susundberg/zephyr-robot-supa2019/3d_parts/stl_files/robot_motor_small_v0.stl

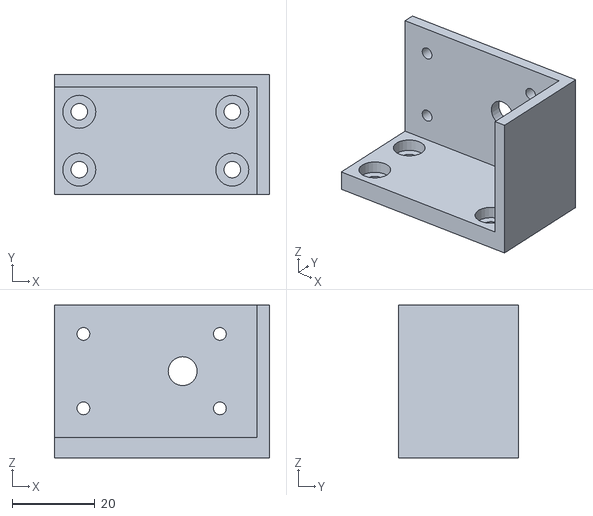
[picture p15: CAD file, 2020-02-02]
3d_parts/stl_files/robot_motor_small_v0.stl
52.0 x 29.0 x 37.0
