susundberg/zephyr-robot-supa2019/3d_parts/stl_files/robot_bumber_mount_f_v0.stl

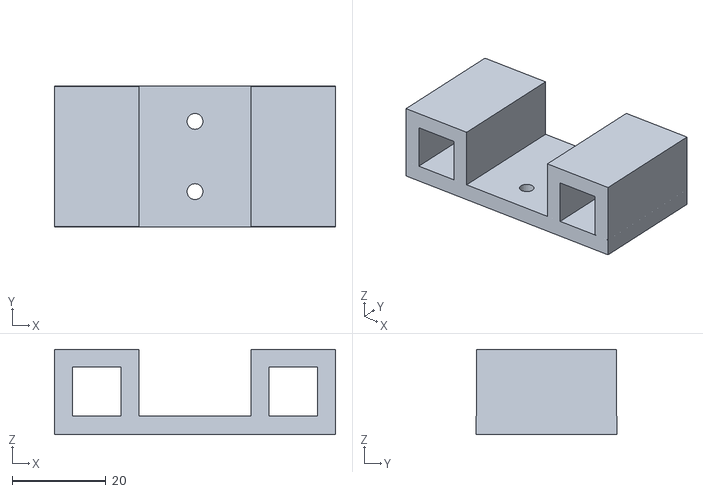
[picture p16: CAD file, 2020-02-02]
3d_parts/stl_files/robot_bumber_mount_f_v0.stl
60.0 x 30.0 x 18.2
