susundberg/zephyr-robot-supa2019/3d_parts/stl_files/robot_supp_mount_v1.stl

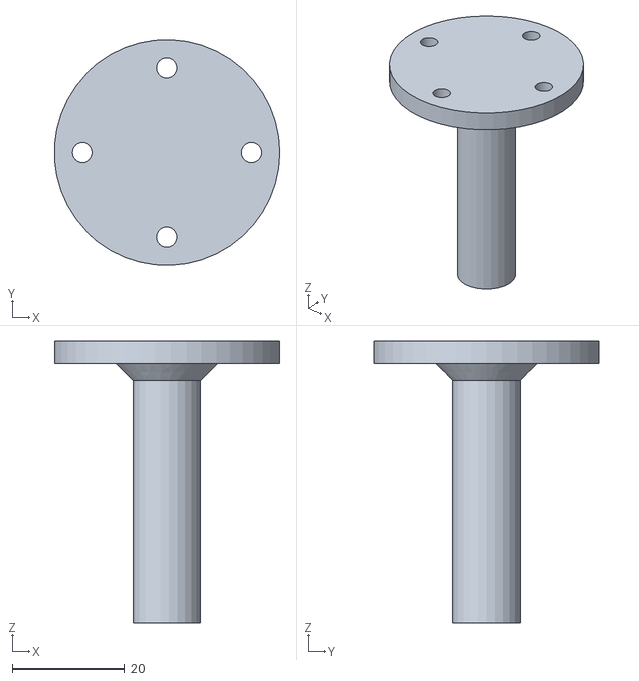
[picture p17: CAD file, 2020-02-02]
3d_parts/stl_files/robot_supp_mount_v1.stl
40.0 x 40.0 x 50.0
