susundberg/zephyr-robot-supa2019/3d_parts/stl_files/bmotor_pads_round_v0.stl

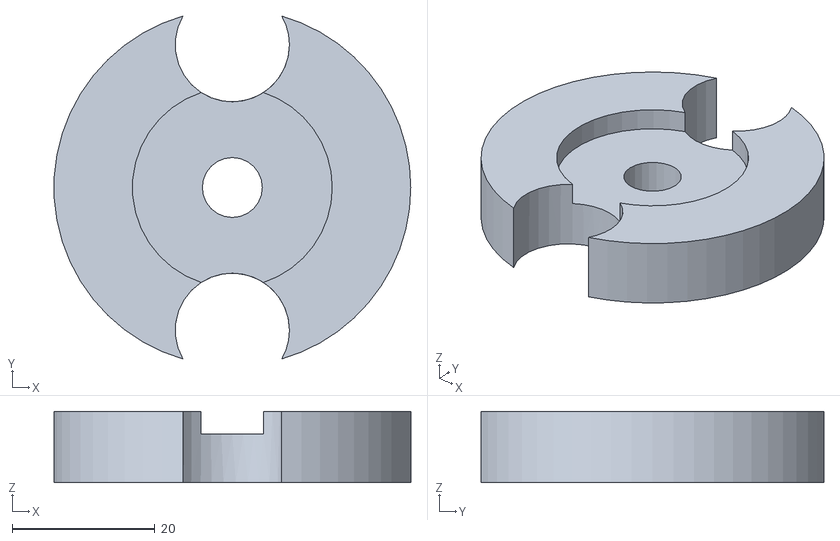
[picture p18: CAD file, 2020-02-02]
3d_parts/stl_files/bmotor_pads_round_v0.stl
50.0 x 48.0 x 10.0
