susundberg/zephyr-robot-supa2019/3d_parts/stl_files/robot_bumber_bumber_v0.stl

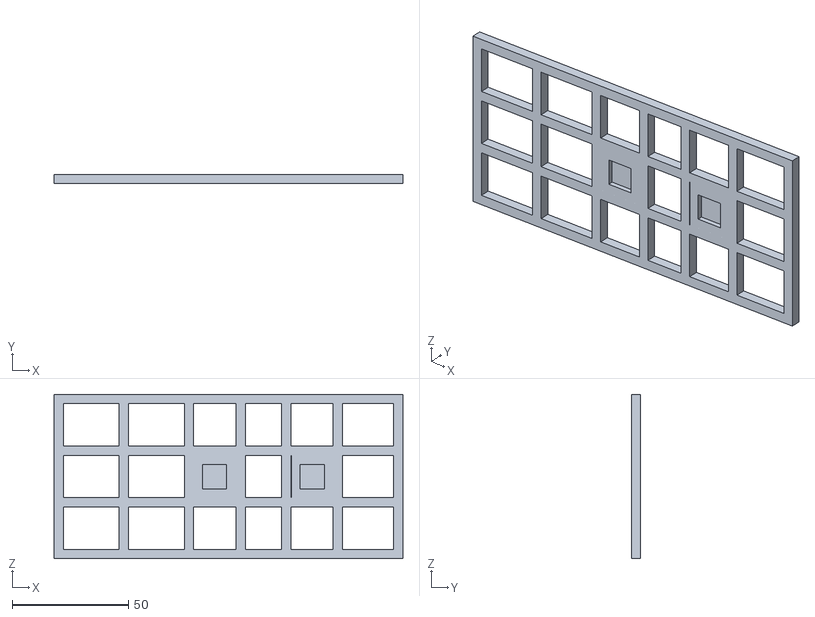
[picture p19: CAD file, 2020-02-02]
3d_parts/stl_files/robot_bumber_bumber_v0.stl
150.0 x 4.00 x 70.6
