susundberg/zephyr-robot-supa2019/schematics/kicad/TMP.sch

## KiCad design schematics/kicad/TMP.sch (2020-06-10)

Schematic: TMP.sch

Parts:
C8: 0.1uF; C_Rect_L4.6mm_W2.0mm_P2.50mm_MKS02_FKP02
C10: 10uF/10V; CP_Radial_Tantal_D4.5mm_P2.50mm
F1: Fuse; Fuseholder_Cylinder-5x20mm_Schurter_0031_8201_Horizontal_Op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
J1: CONN_POWER_IN; TerminalBlock_bornier-2_P5.08mm
U3: LM2596_DC_DC_BUCK_MODULE
U4: LD1117S33TR; TO-220-3_Vertical
