susundberg/zephyr-robot-supa2019/src/motor/motor_ramp.c

#include <math.h>

#define SUPA_MODULE "mor"

#include "../main.h"
#include "motor_ramp.h"

LOG_MODULE_REGISTER( motor_ramp );

#define MINDIFF 0.00001f


static float sqrtf(float square)
{
    float root, last, diff;

    root = square / 3.0f;
    diff = 1.0f;

    if (square <= 0.0f) {
        return 0.0f;
    }

    do {
        last = root;
        root = (root + square / root) / 2.0f;
        diff = root - last;
    } while (diff > MINDIFF || diff < -MINDIFF);

    return root;
}



static float motor_ramp_acc_solve_max_speed( float distance, float max_acc )
{
    const float scalar = (2.0f/3.0f);
    return sqrtf( scalar * distance * max_acc );
}

static float motor_ramp_acc_solve_distance( float max_acc, float speed_diff)
{
    const float scalar = (3.0f/4.0f);
    return (scalar*speed_diff*speed_diff) / max_acc;
}

static float motor_ramp_acc_solve_time(  float max_acc, float speed_diff )
{
    return ( ( 3.0f * speed_diff ) / (2.0f * max_acc) );
}


static float motor_ramp_acc_speed_i( Motor_ramp_acc* acc, float t)
{
    return (1.0f/3.0f) * acc->const_A*(t*t*t) + acc->const_M * t;
}

static float motor_ramp_acc_location_i( Motor_ramp_acc* acc, float t)
{
   float t2 = t*t; 
   return (1.0f/12.0f)*acc->const_A*(t2*t2) + 0.5f*acc->const_M*(t2) - acc->const_B*t;
}

static float motor_ramp_acc_location( Motor_ramp_acc* acc, float t )
{
    t = t - acc->const_T;
    return motor_ramp_acc_location_i(acc,t) - acc->const_D;
}

// static float motor_ramp_acc_speed( Motor_ramp_acc* acc, float t )
// {
//     t = t - acc->const_T;
//     return motor_ramp_acc_speed_i( acc, t ) - acc->const_B;
// }

static void motor_ramp_acc_init( Motor_ramp_acc* acc, float max_acc, float speed_diff )
{
    acc->const_M = max_acc;
    acc->const_T = ( ( 3.0f * speed_diff ) / (4.0f * max_acc) ) ;
    acc->const_A = ( -acc->const_M / (acc->const_T*acc->const_T));
    acc->const_B = motor_ramp_acc_speed_i( acc, -acc->const_T );
    acc->const_D = motor_ramp_acc_location_i( acc, -acc->const_T );
}


void motor_ramp_init( Motor_ramp* ramp, float max_acc, float max_speed, float distance )
{
    
    memset( ramp, 0x00, sizeof(Motor_ramp));
    if ( distance < 0.1f )
    {
        LOG_INF("Distance is smaller than least, assuming zero.");
        return;
    }
    
    float dist_max_speed = motor_ramp_acc_solve_max_speed( distance, max_acc );
    float dist_const_speed; 
    
    if ( dist_max_speed < max_speed )
    {
        LOG_INF("Cannot go full speed, limiting max speed to %d", (int)(dist_max_speed*100.0f));
        max_speed = dist_max_speed ;
        dist_const_speed = 0;
    }
    else
    {
        float ramp_dist = motor_ramp_acc_solve_distance( max_acc, max_speed );
        dist_const_speed = distance - 2*ramp_dist;
        LOG_INF("Full speed available it will take %d -> const dist %d", (int)(ramp_dist*100.0f), (int)(dist_const_speed*100.0f));
        ASSERT( dist_const_speed >= 0.0f );
    }
    
    motor_ramp_acc_init( &ramp->acc_ramp, max_acc, max_speed );
    
    ramp->acc_ramp_len     = motor_ramp_acc_solve_distance( max_acc, max_speed );
    ramp->acc_ramp_time    = motor_ramp_acc_solve_time( max_acc, max_speed );
    ramp->const_ramp_dist  = dist_const_speed;
    ramp->const_ramp_speed = max_speed;
    ramp->const_ramp_time  = dist_const_speed/max_speed;
        
}

float motor_ramp_fulltime( Motor_ramp* ramp )
{
    return 2.0f*ramp->acc_ramp_time + ramp->const_ramp_time;
}


float motor_ramp_location( Motor_ramp* ramp, float t )
{
    
    float loc = 0.0f;
    if ( t < ramp->acc_ramp_time )
        return motor_ramp_acc_location( &ramp->acc_ramp, t );
    
    t   -= ramp->acc_ramp_time;
    loc += ramp->acc_ramp_len;
    
    if ( t < ramp->const_ramp_time )
        return loc + ramp->const_ramp_speed*t;
    
    t   -= ramp->const_ramp_time;
    loc += ramp->const_ramp_dist;
    
    if ( t < ramp->acc_ramp_time )
    {
        float offset = (ramp->const_ramp_speed*t) - motor_ramp_acc_location( &ramp->acc_ramp, t );
        return loc + offset;
    }
    
    return ramp->const_ramp_dist + (2.0f*ramp->acc_ramp_len);
}
