susundberg/zephyr-robot-supa2019/src/main.h

#pragma once

#include <stdlib.h>
#include <string.h>

#include <zephyr.h>
#include <logging/log.h>
#include <sys/printk.h>

void supa_fatal_handler( const char* module, int line );



#ifdef SUPA_MODULE

#define FATAL_ERROR( fmt, ...) { \
   supa_fatal_handler( SUPA_MODULE, __LINE__ ); }
#define ASSERT_ISR(x) { if ( (x) == false ) { supa_fatal_handler( SUPA_MODULE, __LINE__ ); } };
#define ASSERT(x) { if ( (x) == false ) { supa_fatal_handler( SUPA_MODULE, __LINE__ ); } };

#endif

#define HAL_CHECK(x) if ( (x) != HAL_OK) { FATAL_ERROR("HAL call failed!"); };
#define RET_CHECK(x) { int32_t __ret_check = (x); if ( __ret_check != 0 ) { FATAL_ERROR("Call failed: %d", __ret_check ); }};

#define ROUND_INT(x) ( (int32_t)( x + 0.5f) )
#define UNLIKELY(expr) ( __builtin_expect(!!(expr), 0))
#define ABS(x) ((x)<0 ? -(x) : (x))

#define DEV_GET_CHECK( _dev, _name ) { \
    _dev = device_get_binding( _name ); \
    if ( _dev == NULL )\
    {\
        FATAL_ERROR("Cannot find device: %s", _name );\
        return;\
    }\
}

#define OS_DEFAULT_STACKSIZE 512
#define OS_DEFAULT_PRIORITY  7

   
